clararubio20/ESP32_BloquesConstruccion/esp32_admin_html_/include/ESP32_WS.hpp

/*
* Archivo creado por: Clara Rubio Almagro
* Fecha de la ultima modificación: 15/06/2023
* Trabajo Fin de Grado
* Titulación: Sistemas electrónicos
* Universidad de Málaga
* Este archivo guarda las funciones de procesado de WebSockets
* Ambas han sido sacadas de librerías de otros repositorios
*/

void onWsEvent(AsyncWebSocket * server, AsyncWebSocketClient * client, AwsEventType type, void * arg, uint8_t *data, size_t len){ 
	if(type == WS_EVT_CONNECT){
		//Serial.printf("ws[%s][%u] connect\n", server->url(), client->id());
		//client->printf("Hello Client %u :)", client->id());
		client->ping();
	} else if(type == WS_EVT_DISCONNECT){
		//Serial.printf("ws[%s][%u] disconnect: %u\n", server->url(), client->id());
	} else if(type == WS_EVT_ERROR){
		//Serial.printf("ws[%s][%u] error(%u): %s\n", server->url(), client->id(), *((uint16_t*)arg), (char*)data);
	} else if(type == WS_EVT_PONG){
		//Serial.printf("ws[%s][%u] pong[%u]: %s\n", server->url(), client->id(), len, (len)?(char*)data:"");
	} else if(type == WS_EVT_DATA){
		AwsFrameInfo * info = (AwsFrameInfo*)arg;
		String msg = "";
		if(info->final && info->index == 0 && info->len == len){
			if(info->opcode == WS_TEXT){
				for(size_t i=0; i < info->len; i++) {
					msg += (char) data[i];
				}
			} else {
				char buff[3];
				for(size_t i=0; i < info->len; i++) {
					sprintf(buff, "%02x ", (uint8_t) data[i]);
					msg += buff ;
				}
			}

			if(info->opcode == WS_TEXT)
			ProcessRequest(client, msg);
			
		} else {
			//message is comprised of multiple frames or the frame is split into multiple packets
			if(info->opcode == WS_TEXT){
				for(size_t i=0; i < len; i++) {
					msg += (char) data[i];
				}
			} else {
				char buff[3];
				for(size_t i=0; i < len; i++) {
					sprintf(buff, "%02x ", (uint8_t) data[i]);
					msg += buff ;
				}
			}
			Serial.printf("%s\n",msg.c_str());

			if((info->index + len) == info->len){
				if(info->final){
					if(info->message_opcode == WS_TEXT)
					ProcessRequest(client, msg);
				}
			}
		}
	}
}

void InitWebSockets(){
	ws.onEvent(onWsEvent);
	server.addHandler(&ws);
    log(F("\nInfo: WebSocket server iniciado"));
}
